saveswimmer-dot/save-swimmer/diseno_3d/SS-CARCASA-LITE-MOCKUP-V002/README-SS-CARCASA-LITE-MOCKUP-V002.md

# Save Swimmer Lite - mockup carcasa V002

Fecha: 2026-07-12  
Estado: muestra conceptual mas cercana al lenguaje de producto: tracker dorsal compacto, LED frontal, boton/estado, base de fijacion y vista tecnica.

## Medidas de referencia

- Cuerpo objetivo: 74 x 56 x 18 mm.
- Forma: rectangulo redondeado de bajo perfil.
- Ubicacion prevista: espalda alta / zona dorsal, con base o correa.
- Uso de este archivo: imprimir volumen, revisar comodidad, conversar con impresor 3D o disenador industrial.

## Archivos

- `SS-CARCASA-LITE-MOCKUP-V002.png`: lamina visual tecnica.
- `SS-CARCASA-LITE-MOCKUP-V002.stl`: modelo imprimible aproximado.
- `SS-CARCASA-LITE-MOCKUP-V002.scad`: CAD parametrico editable.
- `SS-CARCASA-LITE-MOCKUP-V002.dxf`: contorno 2D superior.
- `SS-CARCASA-LITE-MOCKUP-V002.obj`: referencia simple para visor.

## No resuelve todavia

- Estanqueidad real IP68.
- Junta, tornillos y torque.
- Carga, puerto o carga inductiva.
- Ubicacion exacta de antenas LTE/GPS/BLE.
- Flotabilidad y comportamiento en salinidad.
- Material final, textura, UV, impacto y envejecimiento.
- PCB final y bateria real.
