saveswimmer-dot/save-swimmer/documentos_iso/SS-ACTUALIZACION-ENCUESTA-FORMULARIO-20260709.md

# Save Swimmer - Actualizacion de encuesta por formulario

Fecha: 2026-07-09

Fuente procesada:

C:\Users\Claudia\Downloads\Encuesta Save Swimmer (Respuestas).xlsx

## Resultado

- Respuestas digitales procesadas: 4
- Respuestas nuevas detectadas frente a V001: 2
- Archivo normalizado generado: SS-ENCUESTA-DIGITAL-RESPUESTAS-NORMALIZADAS-V002.csv
- Resumen consolidado generado: SS-RESUMEN-ENCUESTAS-CONSOLIDADO-V002.csv

## Lectura rapida

- La ubicacion en tiempo real sigue como dato mas util en 4/4 respuestas digitales.
- La alerta por nadador detenido sube a 3/4 respuestas digitales.
- Las dos respuestas nuevas agregan emergencia medica como preocupacion principal.
- El organizador de evento aparece con fuerza como receptor de alerta: 3/4 respuestas digitales.
- La membresia queda validada parcialmente: 3/4 aceptan pagar, pero 1/4 indica que no pagaria.
- La preferencia de formato queda dividida: 2/4 pulsera y 2/4 boya.
- NFC/QR de emergencia mantiene aceptacion o interes en 4/4 respuestas digitales.

## Implicancias para producto

1. Mantener la prioridad de seguridad: ubicacion, alerta temprana, inmovilidad/sin avance y escalamiento humano.
2. Para Event, tratar al organizador/rescate/coach como primer receptor operativo.
3. No prometer diagnostico medico; hablar de comportamiento anormal compatible con posible riesgo.
4. Investigar boya como formato/accesorio visible, sin abandonar la ubicacion dorsal prevista para la lectura corporal.
5. Validar membresia con beneficios concretos y alternativa gratuita/simple para familia.

## Cuidado de interpretacion

La muestra digital todavia es pequena. Estos resultados sirven para orientar decisiones y preparar pruebas, no para afirmar conclusiones de mercado.
