saveswimmer-dot/save-swimmer/documentos_iso/SS-ENCUESTA-BREVE-EVENTO-AGUAS-ABIERTAS-V002.docx

SAVE SWIMMER

ENCUESTA BREVE - AGUAS ABIERTAS

Queremos conocer tu experiencia para desarrollar una herramienta realmente útil. Completarla toma menos de 2 minutos. No solicitamos datos sensibles.

1. Tu relación con aguas abiertas:

[ ] Nadador/a [ ] Entrenador/a [ ] Organizador/a [ ] Familiar [ ] Otro: __________________

2. Con que frecuencia participas o entrenas en aguas abiertas?

[ ] Primera vez [ ] Ocasionalmente [ ] Mensualmente [ ] Semanalmente

3. Que situaciones te preocupan más? Marca hasta 3.

[ ] Desorientación [ ] Corriente/oleaje [ ] Quedar rezagado/a

[ ] No ser visible [ ] Inmovilidad o dificultad [ ] Salir lejos del punto esperado

[ ] Que nadie confirme mi regreso [ ] Otra: __________________________

4. Que información sería más útil durante un nado? Marca hasta 3.

[ ] Ubicación aproximada [ ] Movimiento / sin movimiento [ ] Distancia a la costa/base

[ ] Salida de zona segura [ ] Tiempo transcurrido [ ] Confirmación de salida del agua

[ ] Alerta al entrenador/familia [ ] Otra: __________________________

5. Usuarias un dispositivo dorsal pequeño durante el nado?

[ ] Si [ ] Tal vez [ ] No

Lo más importante para usarlo sería: __________________________________________

6. Que podría hacer que no lo uses?

[ ] Incomodidad [ ] Tamaño/peso [ ] Precio [ ] Privacidad [ ] Falsas alertas [ ] Otro: __________

7. En una frase: ¿Que debería resolver Save Swimmer?

________________________________________________________________________________

________________________________________________________________________________

Contacto opcional para recibir avances o participar en pruebas:

Nombre: ______________________________ WhatsApp/correo: ______________________________

[ ] Autorizo que Save Swimmer me contacte sobre avances y pruebas. Puedo solicitar dejar de recibir mensajes.

Instagram/TikTok/Facebook: @saveswimmer | saveswimmer@gmail.com
