saveswimmer-dot/save-swimmer/campana_financiamiento/contenido_01_problema_1280x720.jpg

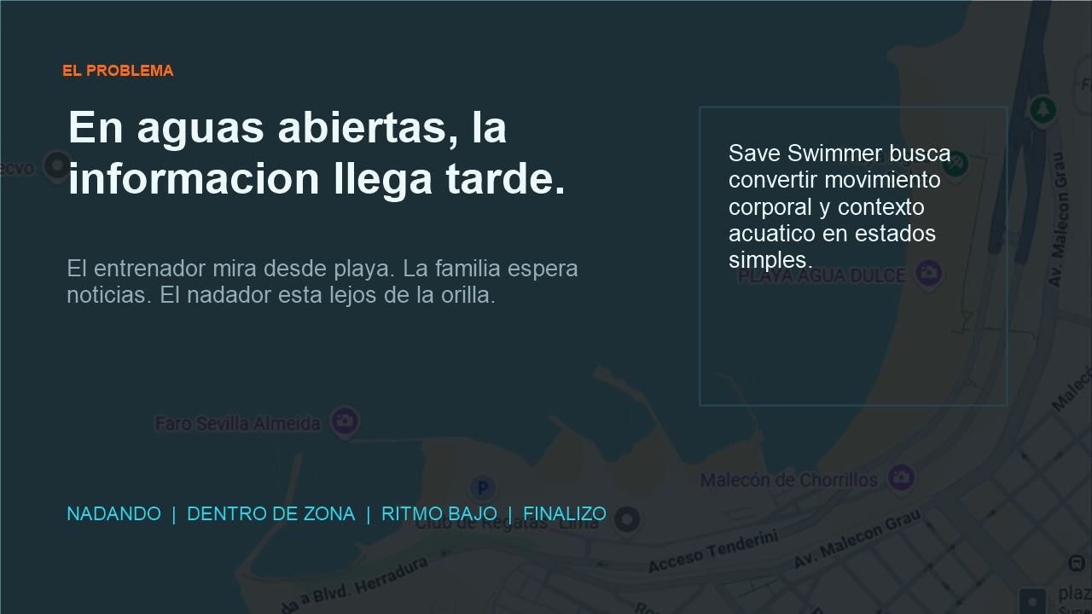
campana_financiamiento/contenido_01_problema_1280x720.jpg
