saveswimmer-dot/save-swimmer/campana_financiamiento/contenido_02_avance_real_1280x720.jpg

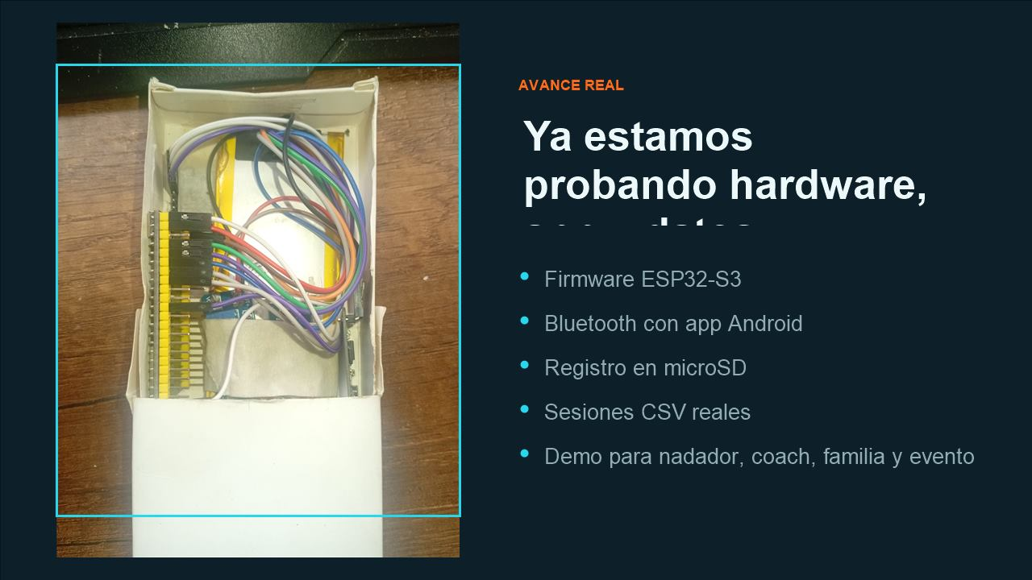
campana_financiamiento/contenido_02_avance_real_1280x720.jpg
