saveswimmer-dot/save-swimmer/campana_financiamiento/contenido_03_meta_1280x720.jpg

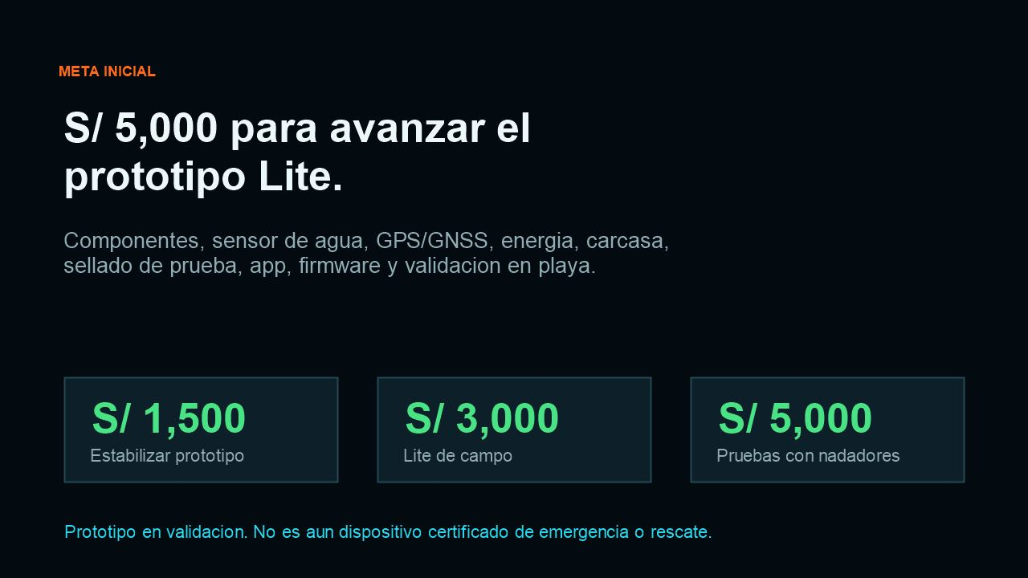
campana_financiamiento/contenido_03_meta_1280x720.jpg
