saveswimmer-dot/save-swimmer/campana_financiamiento/foto_gps_neo_m9n_v001.jpg

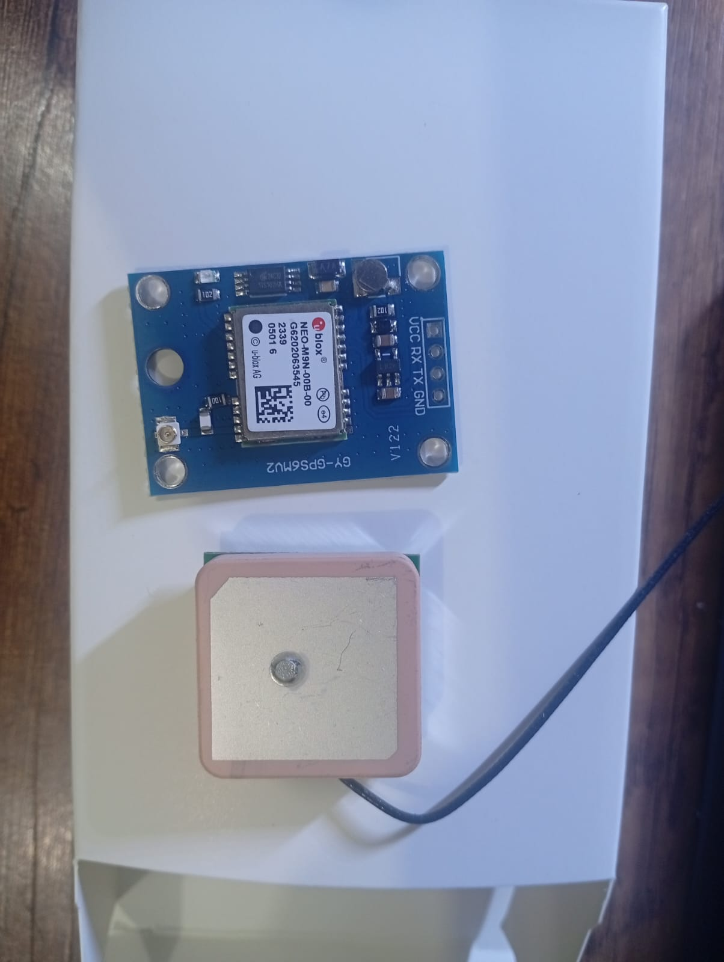
campana_financiamiento/foto_gps_neo_m9n_v001.jpg
