saveswimmer-dot/save-swimmer/campana_financiamiento/foto_ina219_v001.jpg

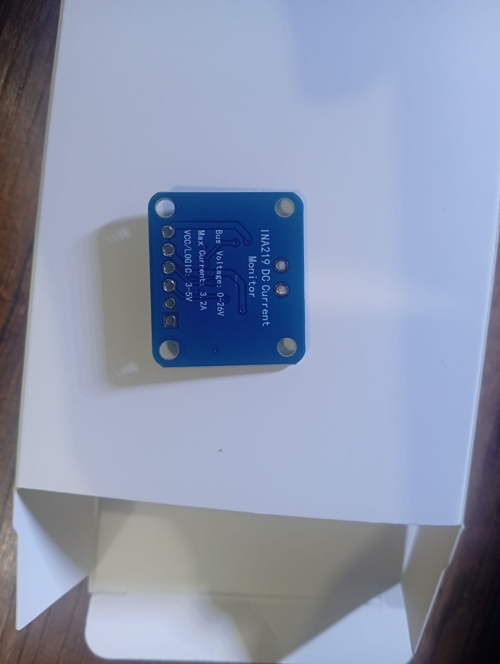
campana_financiamiento/foto_ina219_v001.jpg
