saveswimmer-dot/save-swimmer/campana_financiamiento/portada_startfund_save_swimmer_1920x1080.jpg

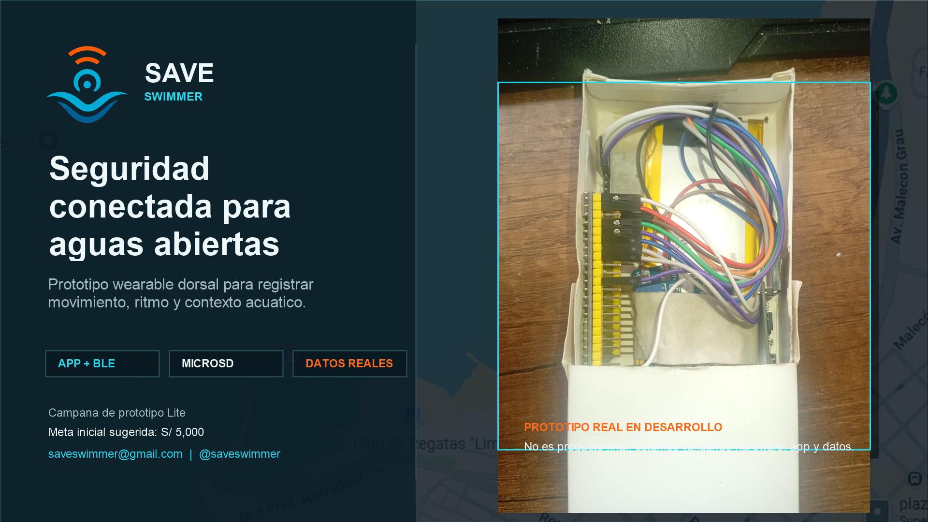
campana_financiamiento/portada_startfund_save_swimmer_1920x1080.jpg
