saveswimmer-dot/save-swimmer/campana_financiamiento/post_avance_plin_1080x1080_v002.png

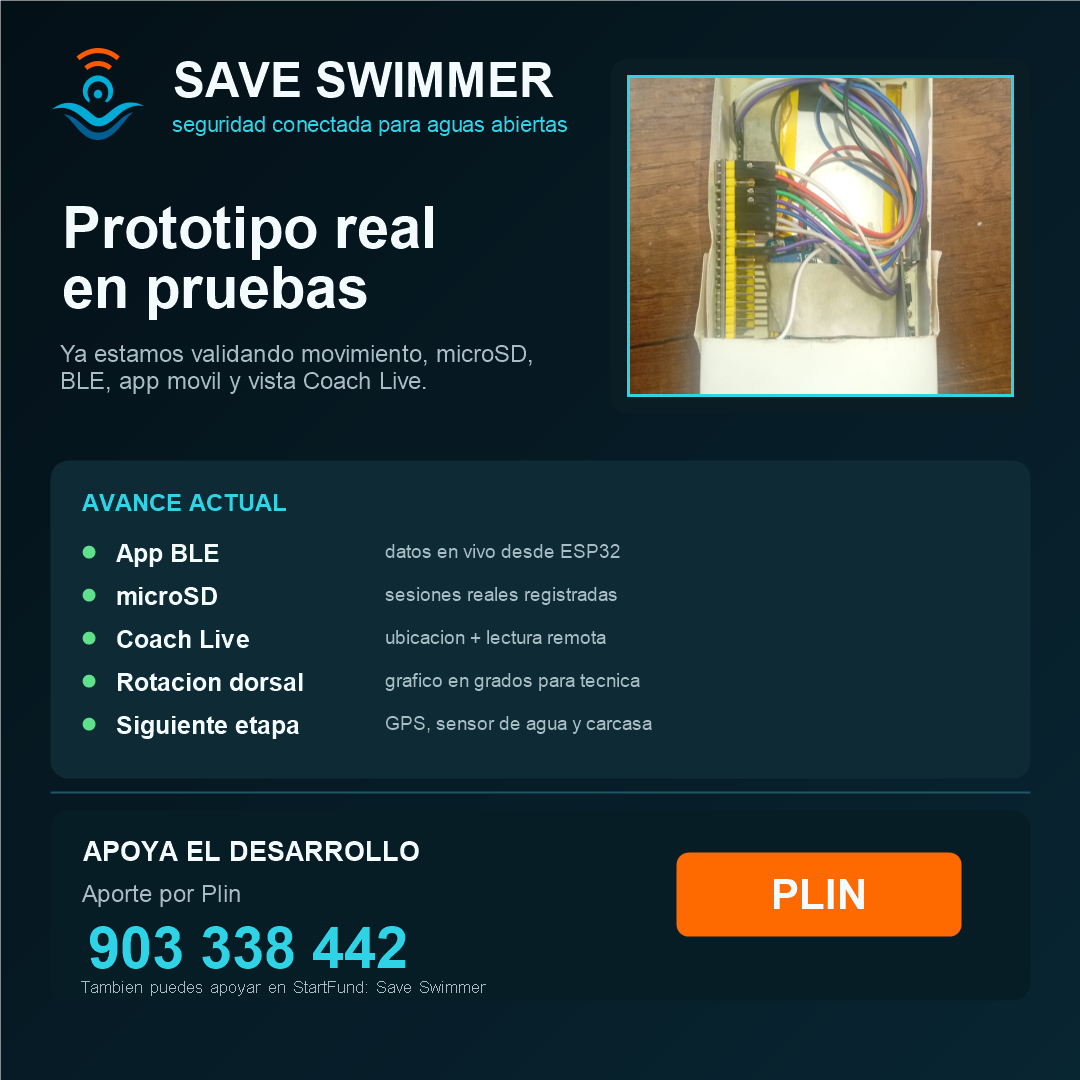
campana_financiamiento/post_avance_plin_1080x1080_v002.png
