saveswimmer-dot/save-swimmer/campana_financiamiento/post_redes_beneficios_nuevas_compras_v001.png

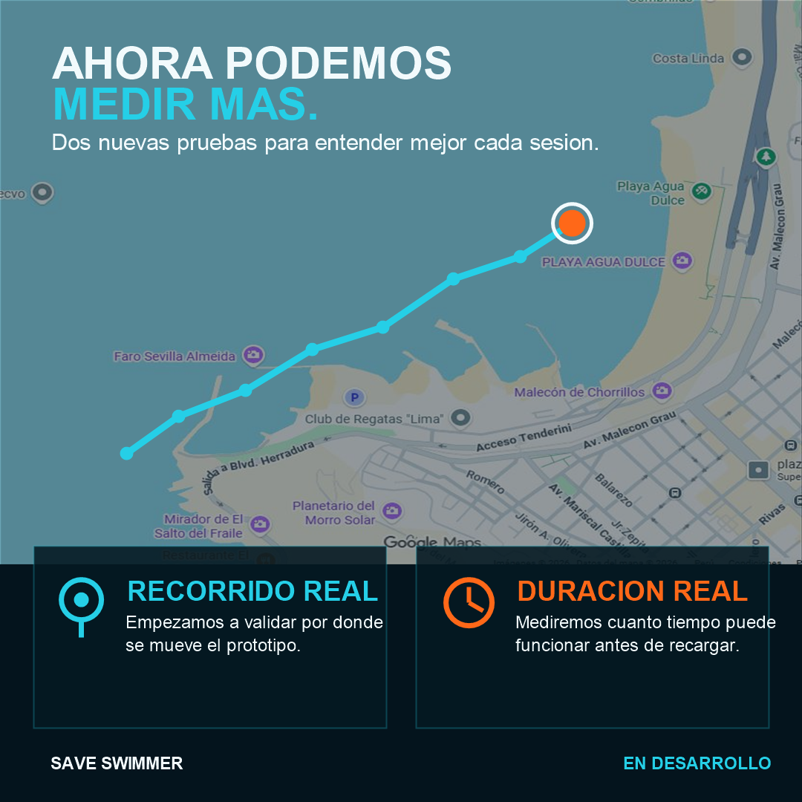
campana_financiamiento/post_redes_beneficios_nuevas_compras_v001.png
