saveswimmer-dot/save-swimmer/campana_financiamiento/post_redes_nuevas_herramientas_v001.png

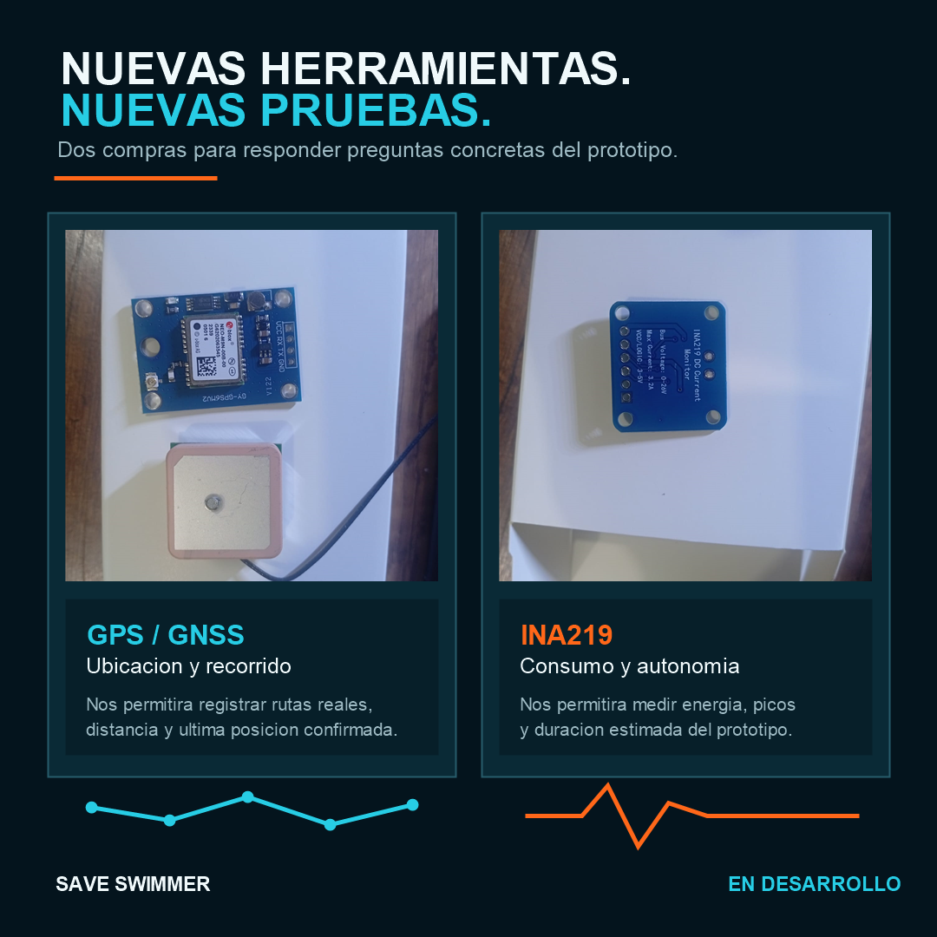
campana_financiamiento/post_redes_nuevas_herramientas_v001.png
