saveswimmer-dot/save-swimmer/campana_financiamiento/post_redes_ruta_confirmada_v001.png

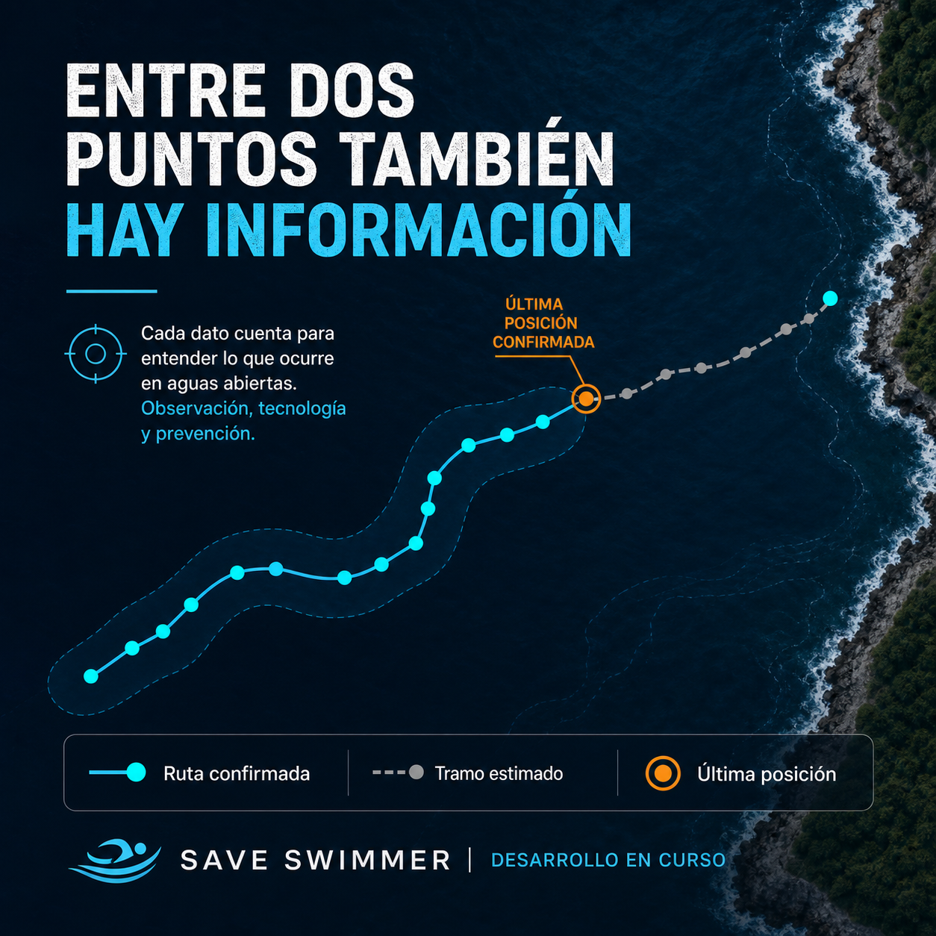
campana_financiamiento/post_redes_ruta_confirmada_v001.png
