saveswimmer-dot/save-swimmer/campana_financiamiento/recompensa_01_impulso_480x270.jpg

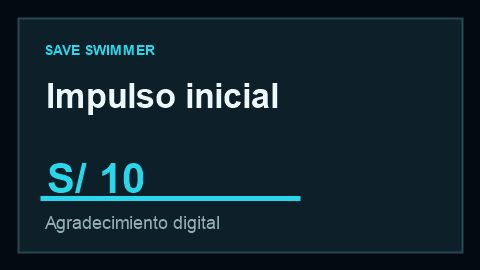
campana_financiamiento/recompensa_01_impulso_480x270.jpg
