saveswimmer-dot/save-swimmer/campana_financiamiento/recompensa_02_ola_480x270.jpg

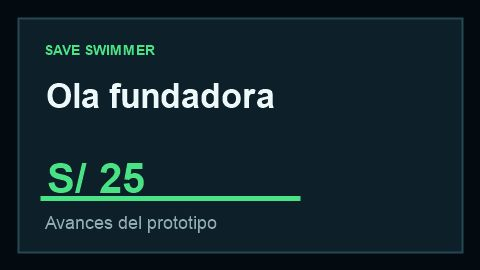
campana_financiamiento/recompensa_02_ola_480x270.jpg
