saveswimmer-dot/save-swimmer/campana_financiamiento/recompensa_03_aliado_480x270.jpg

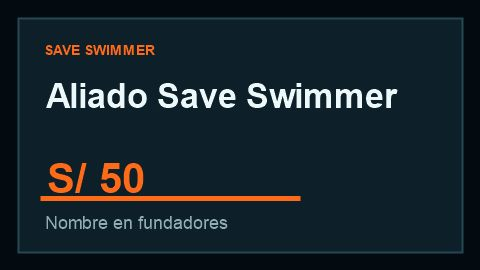
campana_financiamiento/recompensa_03_aliado_480x270.jpg
