saveswimmer-dot/save-swimmer/campana_financiamiento/recompensa_04_equipo_480x270.jpg

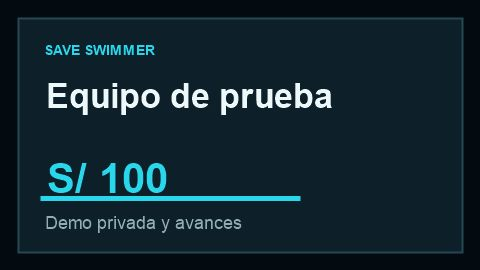
campana_financiamiento/recompensa_04_equipo_480x270.jpg
