saveswimmer-dot/save-swimmer/campana_financiamiento/recompensa_05_coach_480x270.jpg

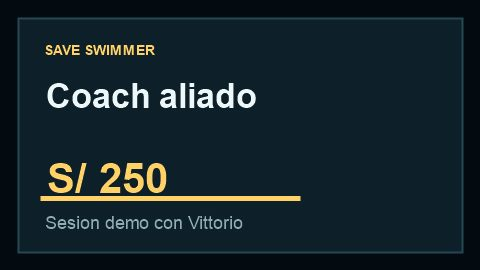
campana_financiamiento/recompensa_05_coach_480x270.jpg
