saveswimmer-dot/save-swimmer/redes/SS-POST-AVANCE-PROTOTIPO-V001.png

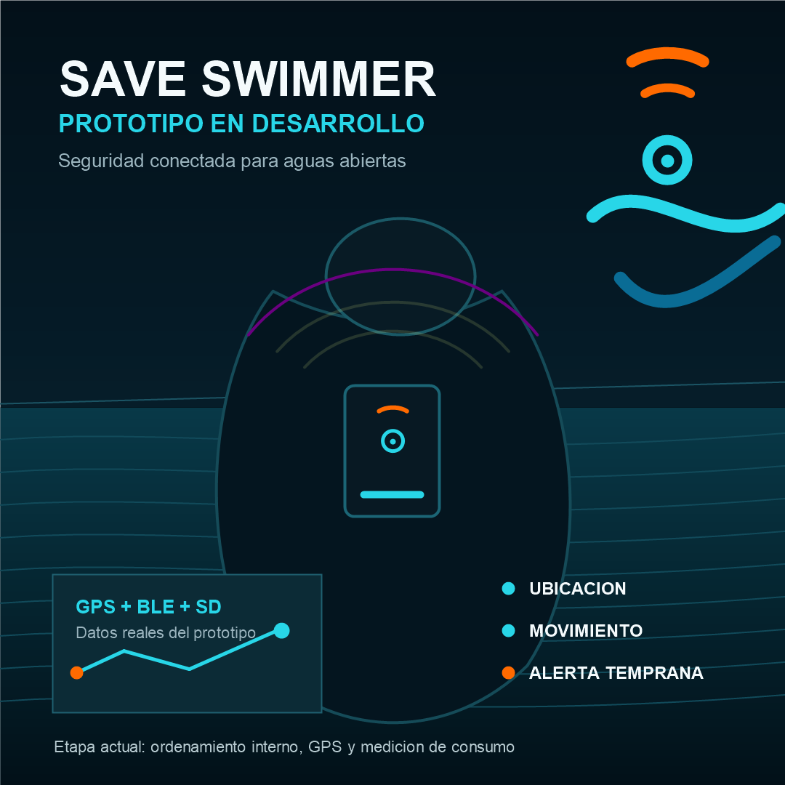
redes/SS-POST-AVANCE-PROTOTIPO-V001.png
