saveswimmer-dot/save-swimmer/redes/SS-POST-AVANCE-REAL-PROTOTIPO-V002.png

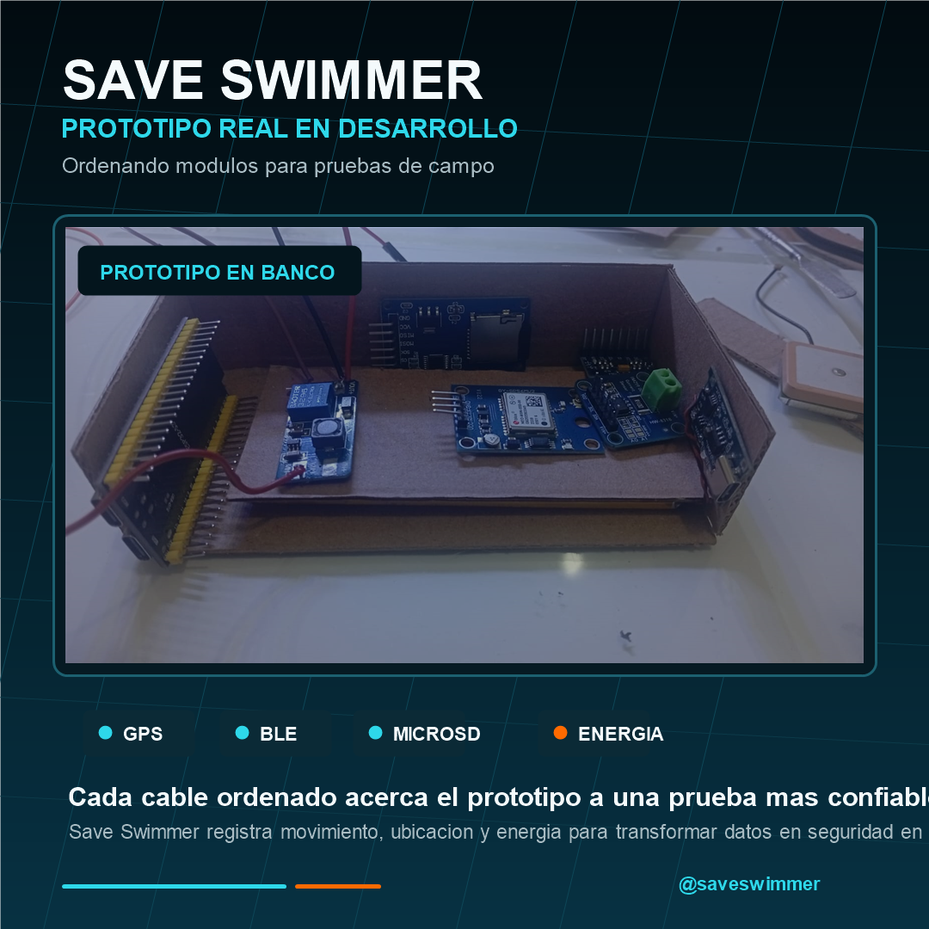
redes/SS-POST-AVANCE-REAL-PROTOTIPO-V002.png
