saveswimmer-dot/save-swimmer/redes/SS-POST-ETAPA-TAMANO-V003.png

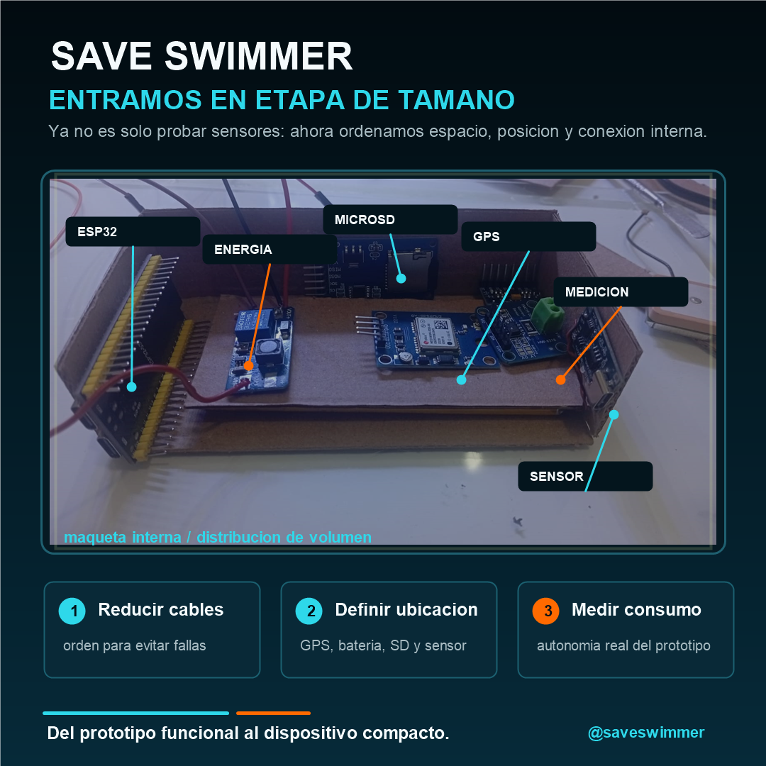
redes/SS-POST-ETAPA-TAMANO-V003.png
