saveswimmer-dot/save-swimmer/redes/SS-POST-SEGUIR-PROYECTO-V005.png

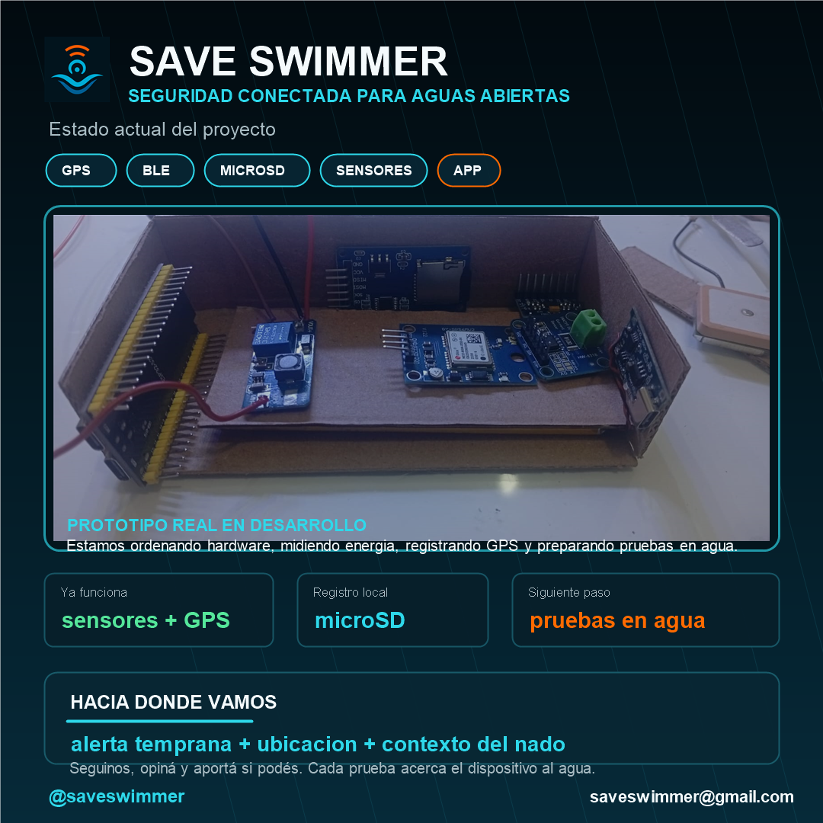
redes/SS-POST-SEGUIR-PROYECTO-V005.png
