saveswimmer-dot/save-swimmer/redes/SS-POST-SEGUIR-PROYECTO-V006.png

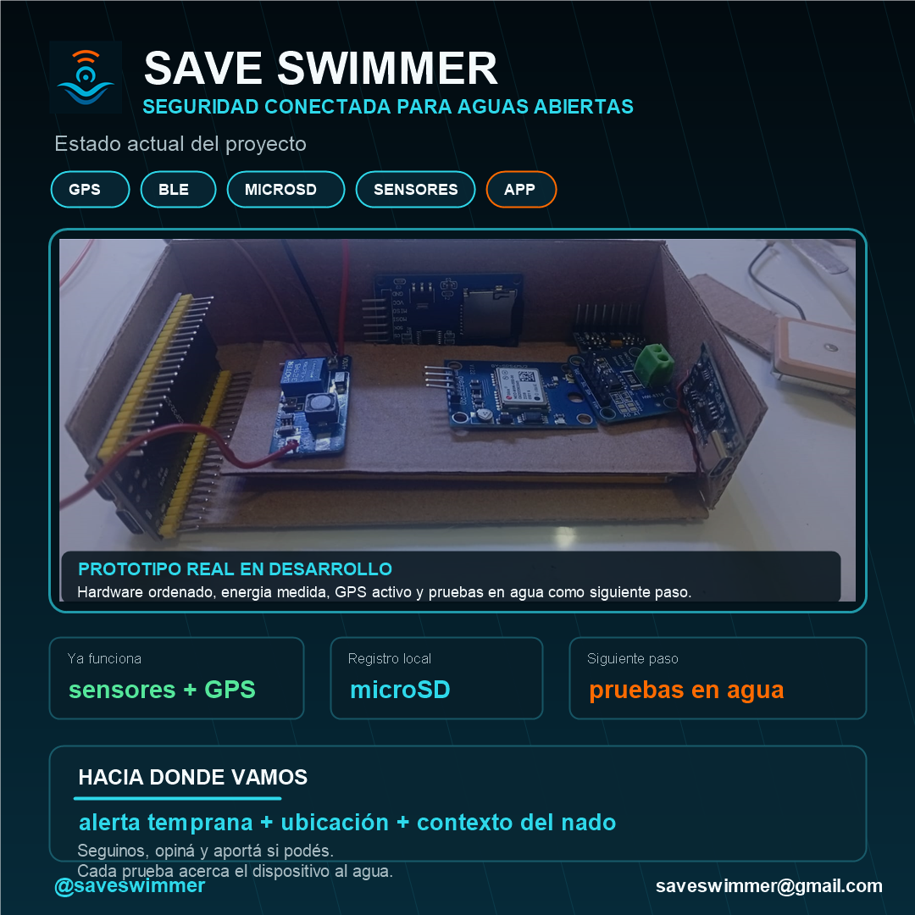
redes/SS-POST-SEGUIR-PROYECTO-V006.png
