saveswimmer-dot/save-swimmer/redes/SS-POST-TELEMETRIA-EN-VIVO-V008.png

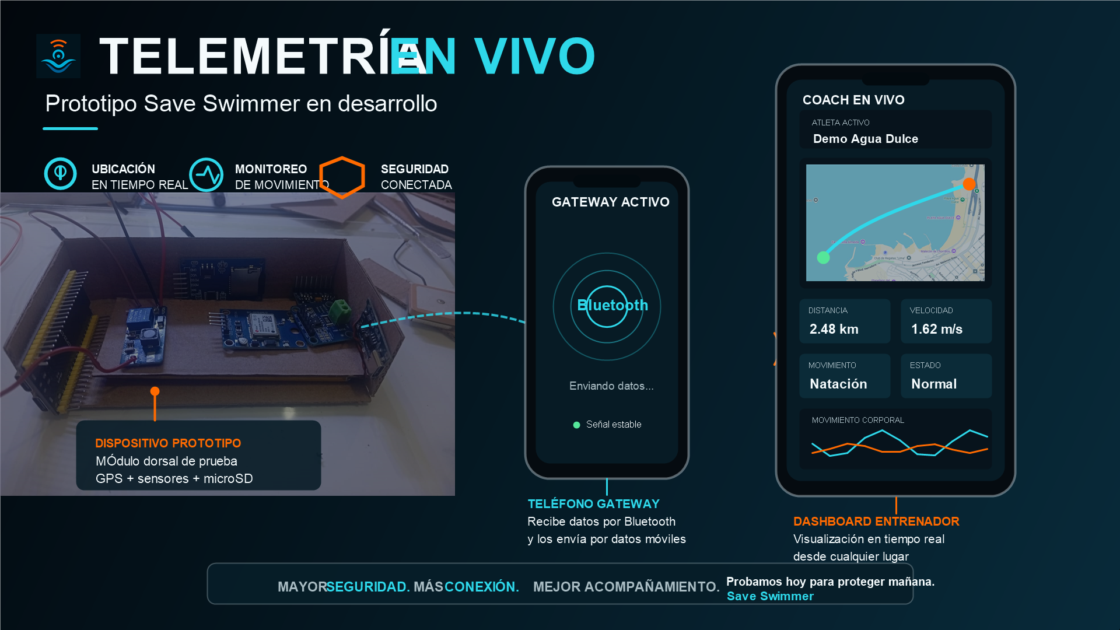
redes/SS-POST-TELEMETRIA-EN-VIVO-V008.png
