saveswimmer-dot/save-swimmer/social_posts/output/SS-POST-VALIDACION-PISCINA-V001.png

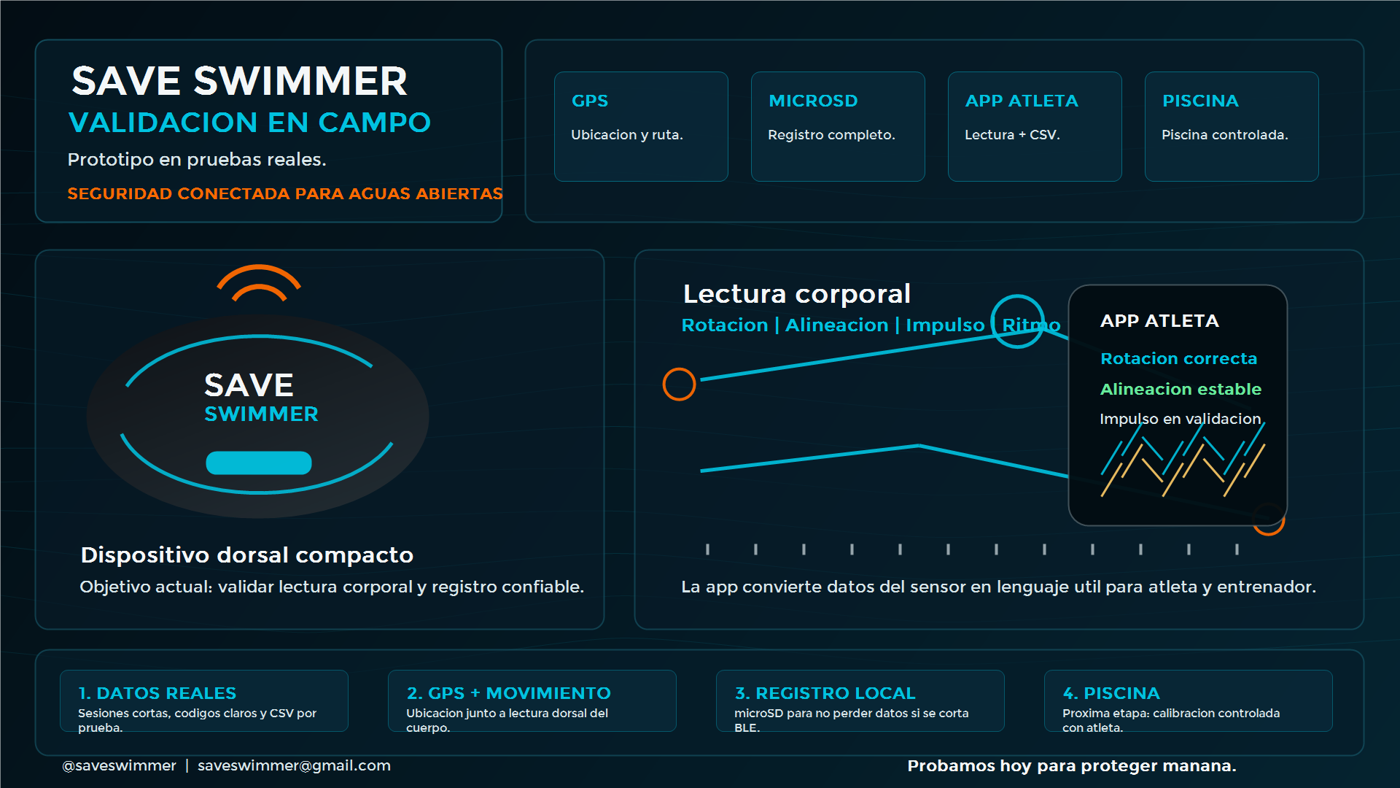
social_posts/output/SS-POST-VALIDACION-PISCINA-V001.png
