saveswimmer-dot/save-swimmer/hardware_design/SS-PROTOTIPO-ACTUAL-KICAD-V001/SS-PROTOTIPO-ACTUAL-V001.sch

## KiCad design hardware_design/SS-PROTOTIPO-ACTUAL-KICAD-V001/SS-PROTOTIPO-ACTUAL-V001.sch (2026-07-23)

Schematic: SS-PROTOTIPO-ACTUAL-V001.sch

Parts:
BT1: BATERIA_LIPO_3V7
C1: 1000uF_16V_RECOMENDADO
C2, C3: 100nF_104
J1: ENTRADA_CARGA_5V
SW1: INTERRUPTOR_GENERAL
U1: TP4056_PROTEGIDO
U2: MT3608_AJUSTADO_5V
U3: ESP32-S3_DEVKIT_N16R8
U3B: ESP32_CONTINUACION
U4: MPU6050_MODULO
U5: MICROSD_SPI_CONVERSION_3V3

Notes on the sheet:
ENERGIA Y CARGA
CONTROL Y SENSORES
Flujo de energia actual: LiPo -> TP4056 protegido -> interruptor -> MT3608 ajustado a 5.0V -> ESP32-S3 + microSD
ADVERTENCIA: verificar polaridad y ajustar MT3608 antes de conectar el ESP32. No cargar una bateria danada o usada sin supervision.
C1 1000uF recomendado cerca de la carga de 5V. C2/C3 son ceramicos 104 = 100nF.
El MPU6050 usa 3V3. El modulo microSD probado usa 5V por incluir regulador/conversion de nivel.
GPIO SPI confirmados por firmware V044: CS=10, MOSI=11, SCK=12, MISO=13.
I2C propuesto para documentacion: SDA=GPIO8, SCL=GPIO9. Confirmar cableado real antes de usar este plano como referencia.
1 IN+
2 IN-
3 B+
4 B-
5 OUT+
6 OUT-
3 OUT+
4 OUT-
VCC
GND
SCL
SDA
AD0=GND
INT no conectado
VCC 5V probado
MOSI
SCK
MISO
CONEXIONES CONFIRMADAS
microSD SPI: GPIO10 CS / GPIO11 MOSI / GPIO12 SCK / GPIO13 MISO
MPU6050 detectado en direccion I2C 0x68
Alimentacion en pruebas de bateria: MT3608 = 5.06V; microSD conectada a 5V
BLE integrado en ESP32-S3; no requiere cableado adicional
